MOSH-Insa-Toulouse/Delorme_Mendes_Gas_Sensor/Final Version/Images/LTC1050 lib.PNG

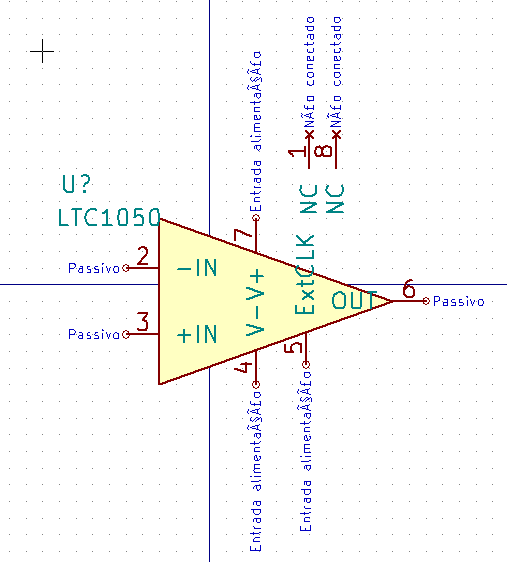
Final Version/Images/LTC1050 lib.PNG
