MOSH-Insa-Toulouse/Delorme_Mendes_Gas_Sensor/Final Version/Images/PCB 3D Up side.PNG

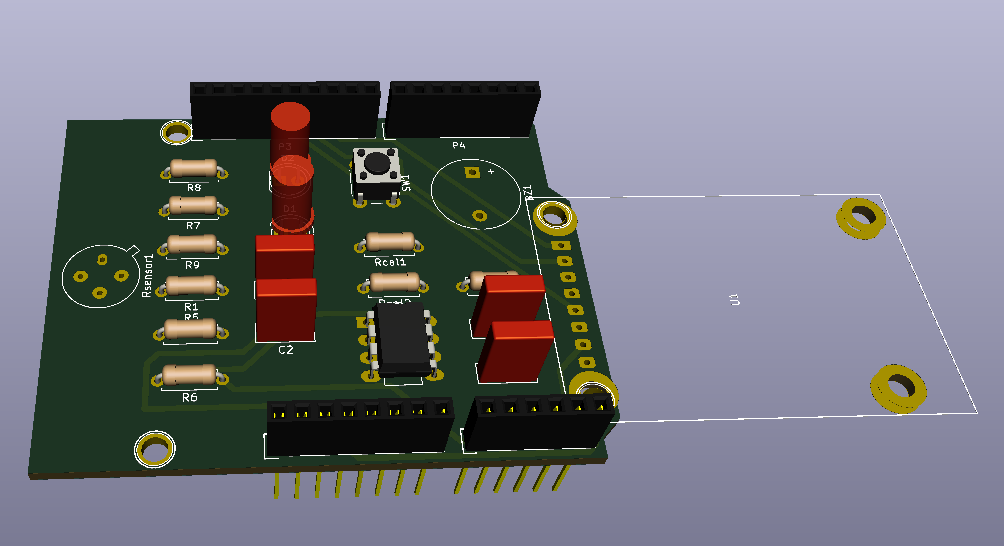
Final Version/Images/PCB 3D Up side.PNG
