MOSH-Insa-Toulouse/Delorme_Mendes_Gas_Sensor/Final Version/Images/RN2483 lib.PNG

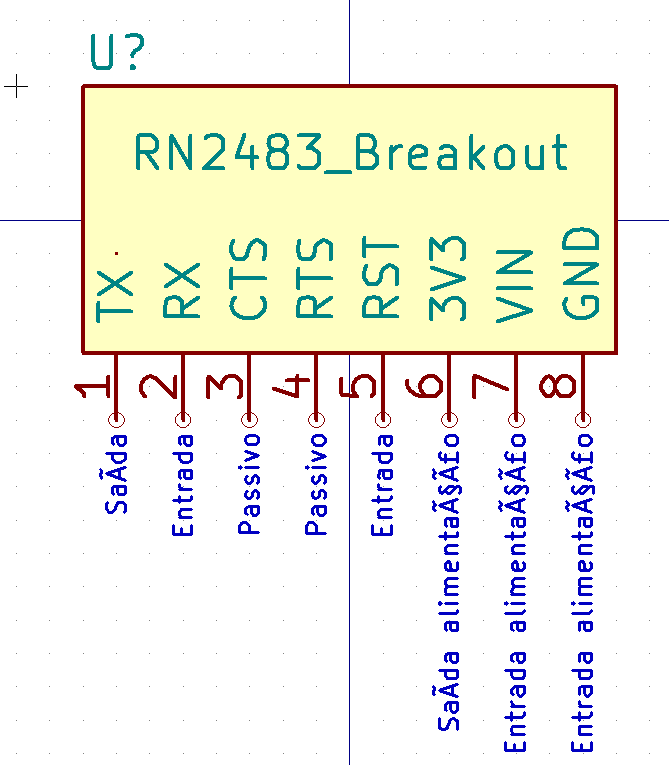
Final Version/Images/RN2483 lib.PNG
