MOSH-Insa-Toulouse/Delorme_Mendes_Gas_Sensor/Images/3D View.PNG

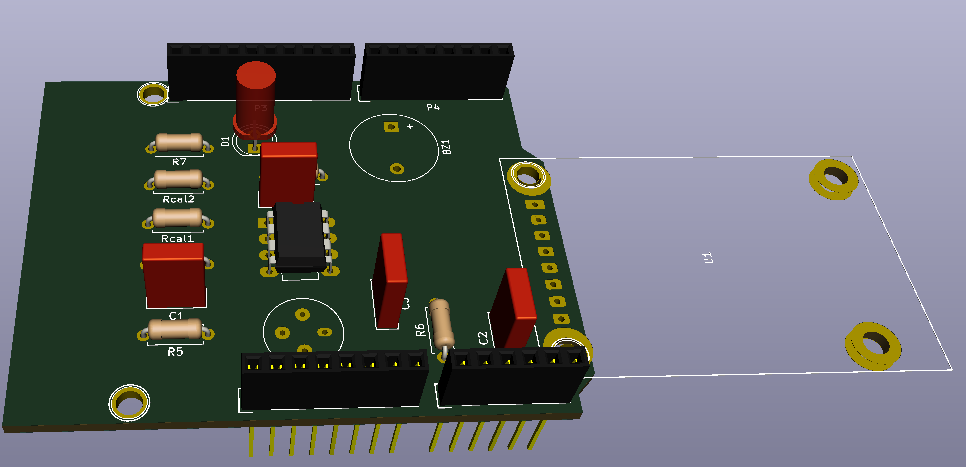
Images/3D View.PNG
