MOSH-Insa-Toulouse/Delorme_Mendes_Gas_Sensor/Images/Capture.PNG

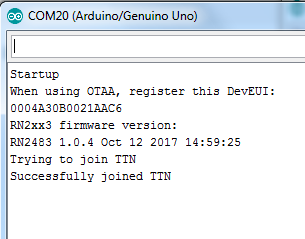
Images/Capture.PNG
